wjduenow/mask-cam/back_analysis.png

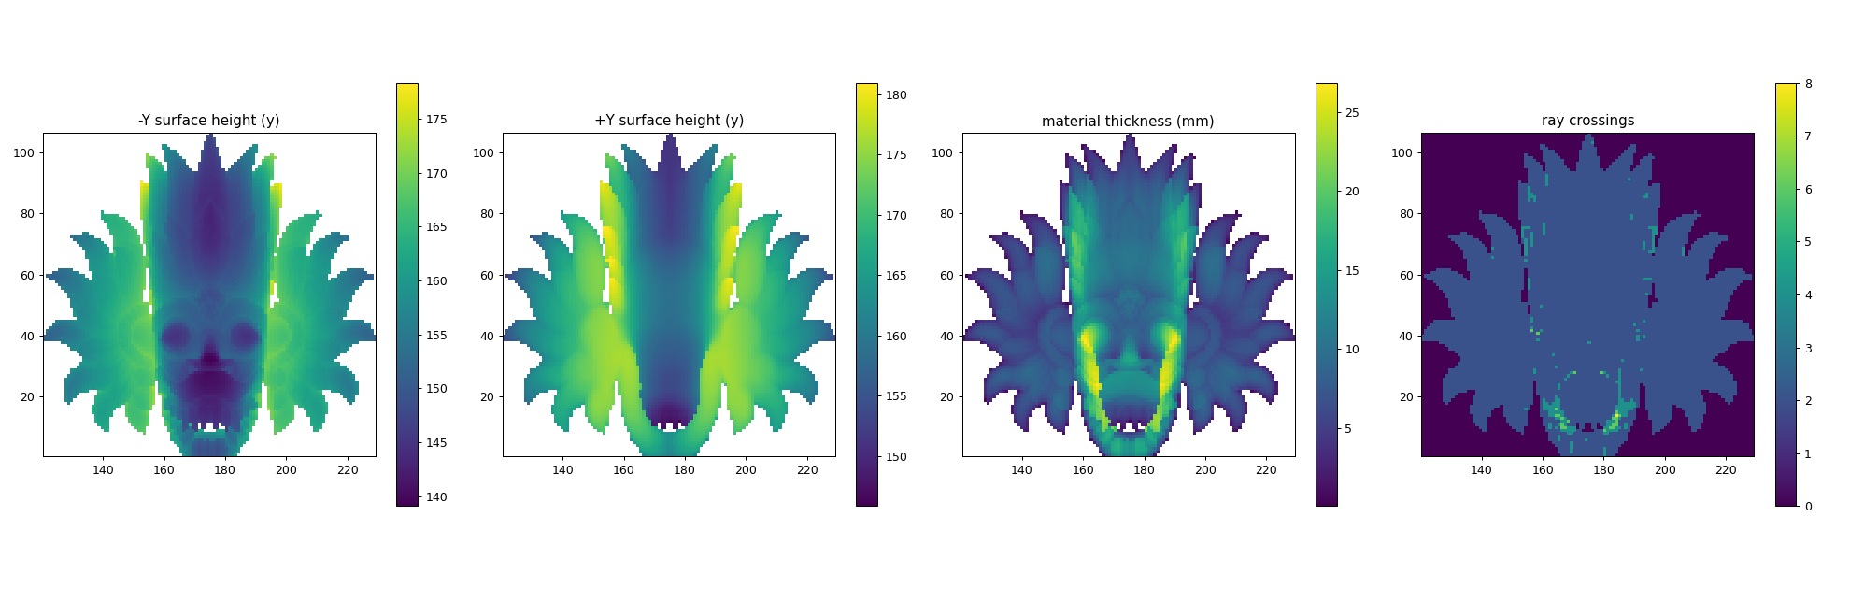
back_analysis.png
