wjduenow/mask-cam/bay.png

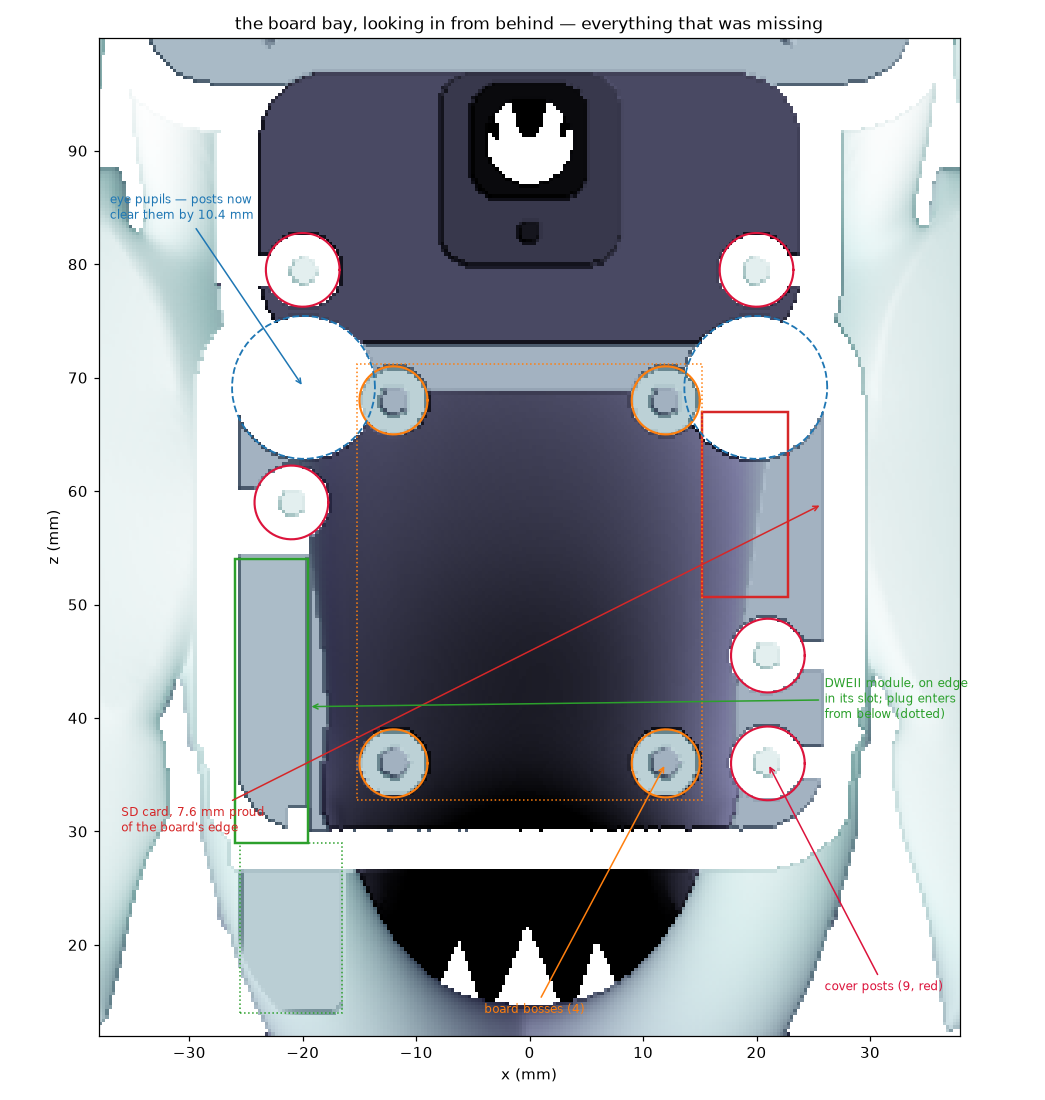
bay.png
