wjduenow/mask-cam/cover_vents.png

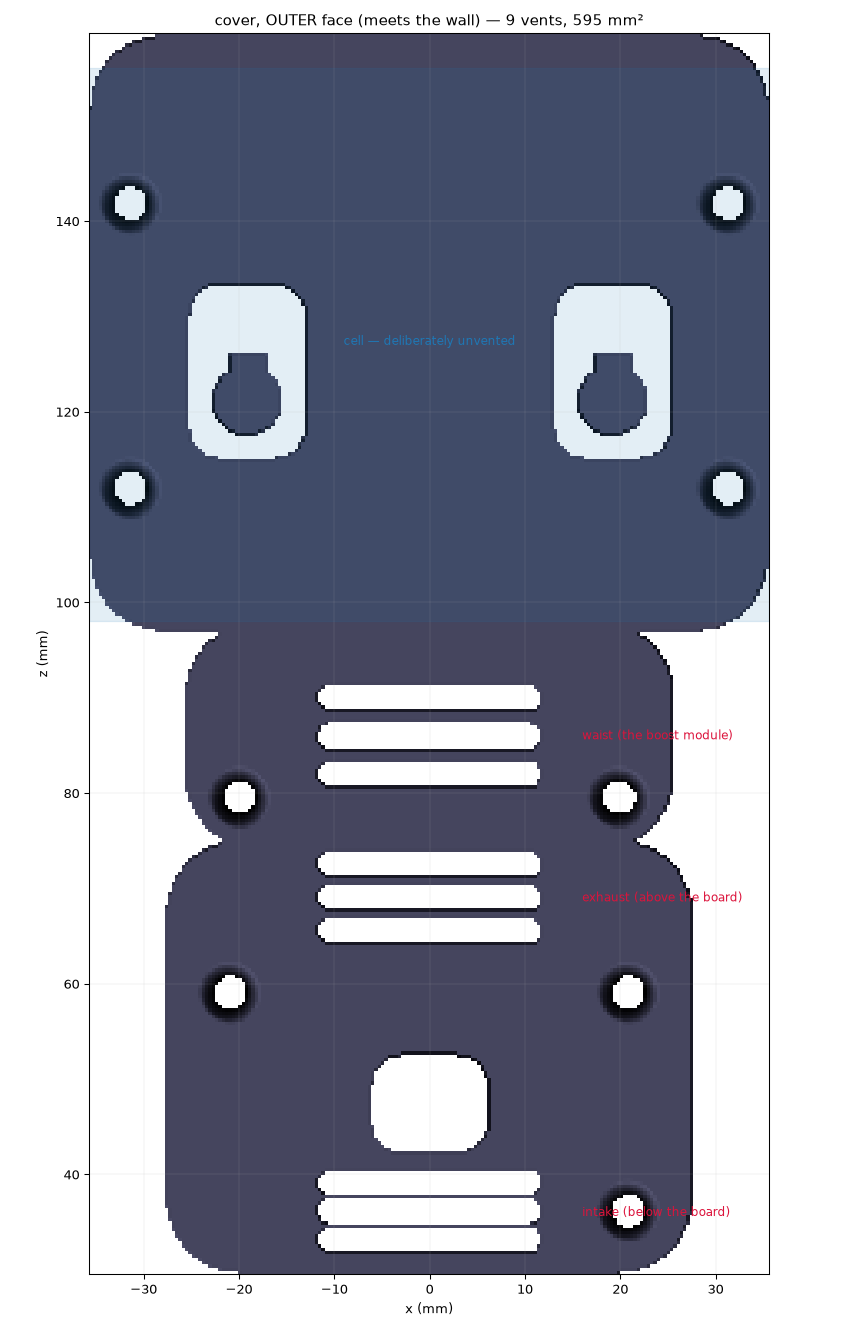
cover_vents.png
