wjduenow/mask-cam/mask_cam_preview.png

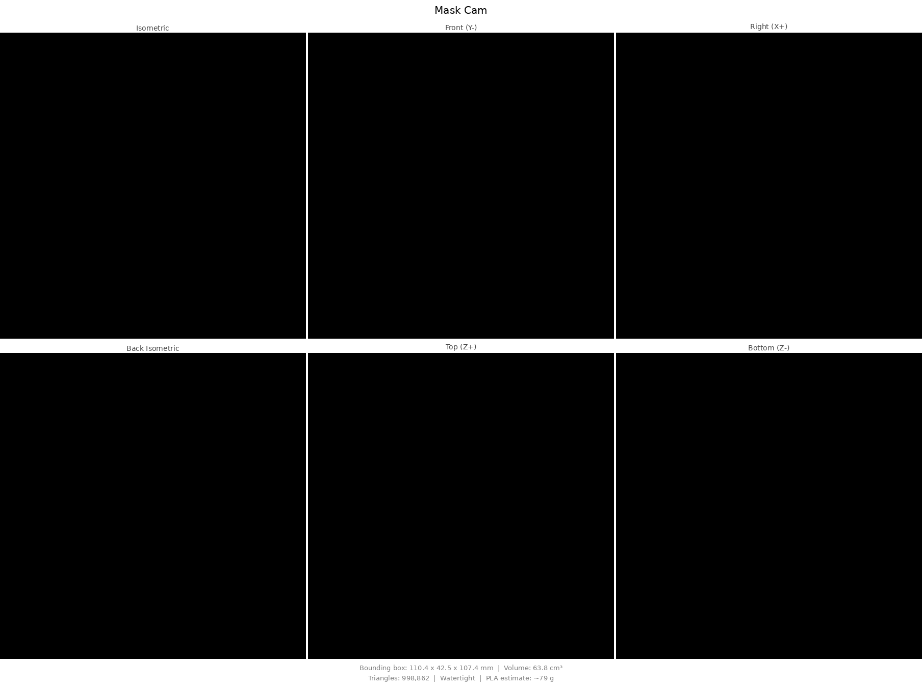
mask_cam_preview.png
