wjduenow/mask-cam/pocket_section.png

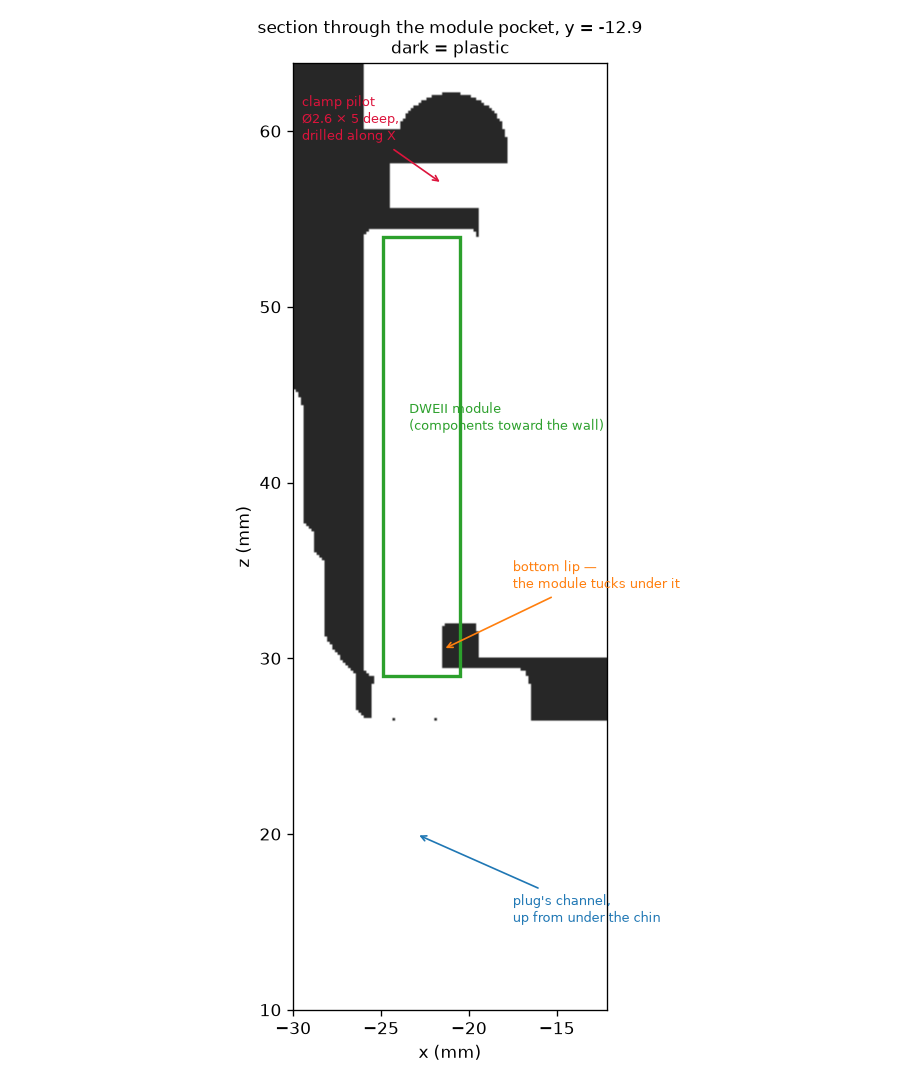
pocket_section.png
